OxfordIonTrapGroup/stabilizer_current_sense/afe.asc

C1: cap; 4.7n
C2: cap; 47n
C3: cap; 4.7n
C4: cap; 8.2p
C5: cap; 43p
R1: res; 10k
R2: res; 16R
R3: res; 10k
R4: res; 16R
R5: res; 10R
R6: res; 1k
R7: res; 1k
R8: res; 1k
R9: res; 1k
R10: res; 100k
R11: res; 1k
R12: res; 20k
R13: res; 1k
U1: LT1007
U2: LT1007
U3: LT1007
U4: LT1007
U5: LT1007
U6: LT1007
V1: voltage; 0
Vcc: voltage; 12V
Vdd: voltage; 12V
Named nets: Vcc, Vdd, 0, Verr
.noise V(Verr) V1 dec 100 100 10000000
